PBL-Pick-By-Light/ES-hardware-design/Documentation/Users Guide/JPG/FloraNeopixel.jpg

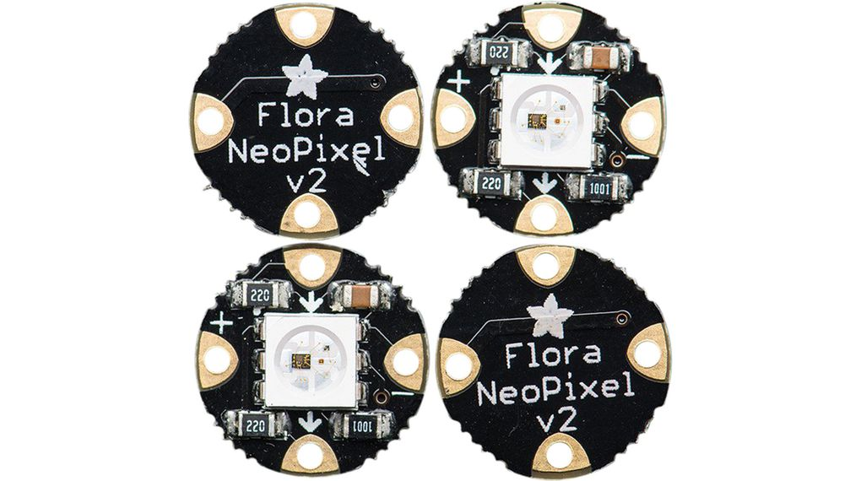
Documentation/Users Guide/JPG/FloraNeopixel.jpg
