PBL-Pick-By-Light/ES-hardware-design/Documentation/Users Guide/JPG/FloraNeopixelArrows.jpg

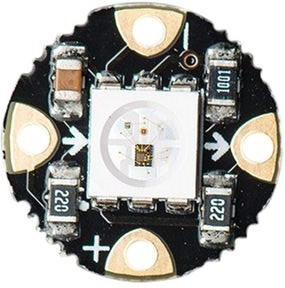
Documentation/Users Guide/JPG/FloraNeopixelArrows.jpg
