PBL-Pick-By-Light/ES-hardware-design/Documentation/Users Guide/JPG/FloraNeopixelBack.jpg

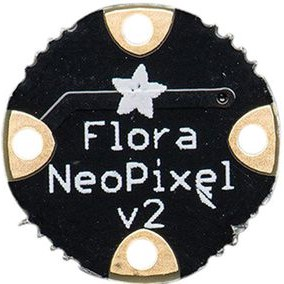
Documentation/Users Guide/JPG/FloraNeopixelBack.jpg
