PBL-Pick-By-Light/ES-hardware-design/Documentation/Users Guide/Render/Back.png

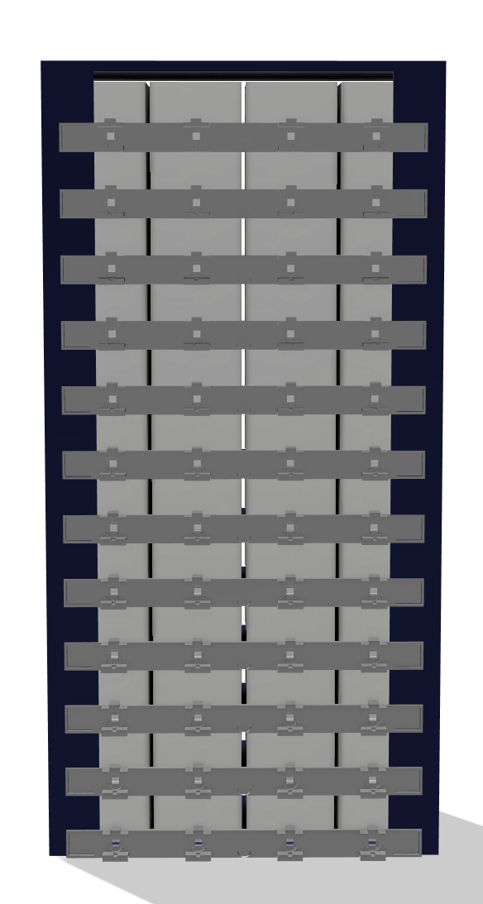
Documentation/Users Guide/Render/Back.png
