PBL-Pick-By-Light/ES-hardware-design/Documentation/Testing/1LEDPerCompartment.jpg

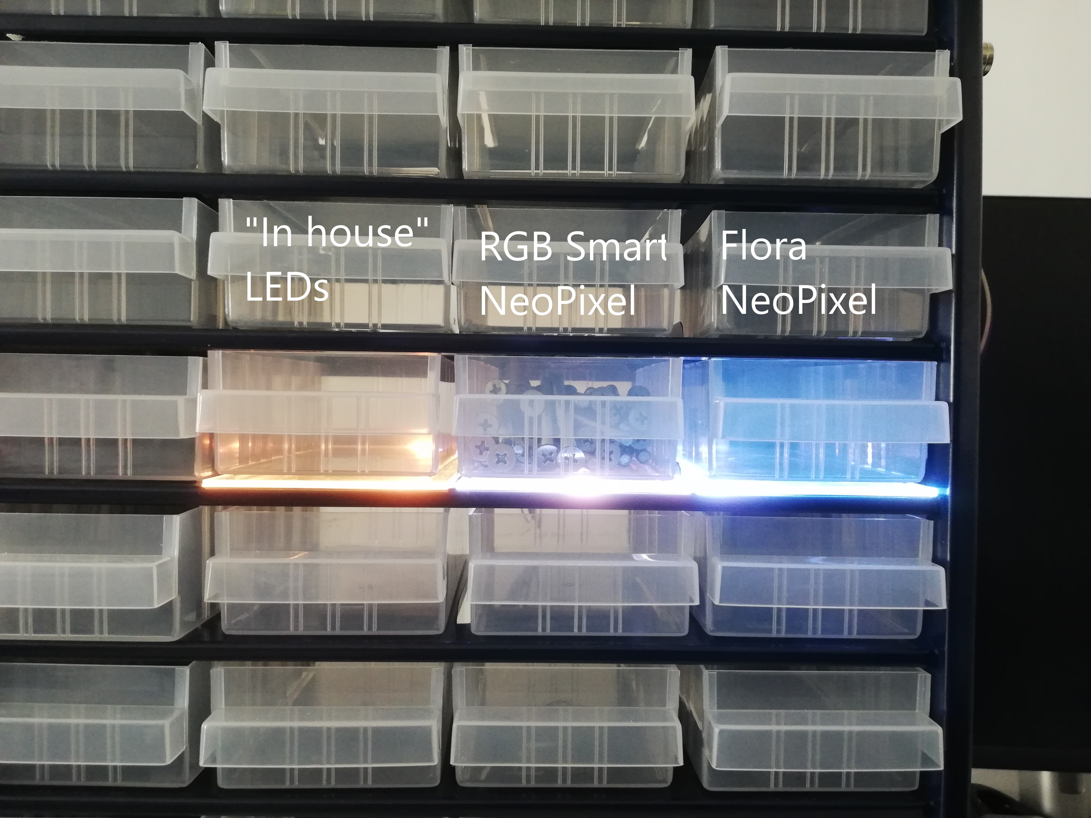
Documentation/Testing/1LEDPerCompartment.jpg
