PBL-Pick-By-Light/ES-hardware-design/Documentation/Testing/2LEDsPerCompartment.jpg

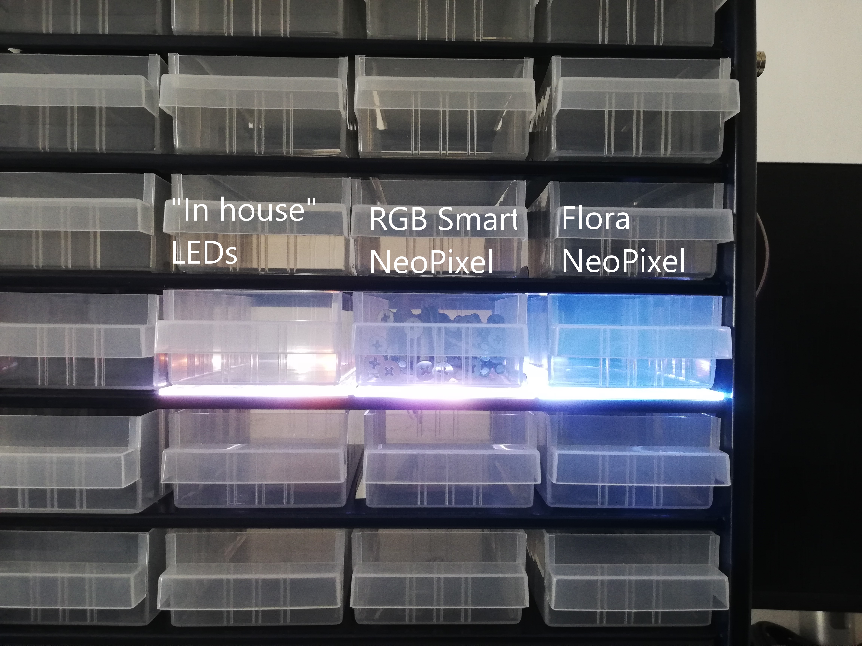
Documentation/Testing/2LEDsPerCompartment.jpg
